FedeJack06/RadioWeatherStation/Schematics/Schematic_master.kicad_sch

## KiCad design Schematics/Schematic_master.kicad_sch (2022-10-13)

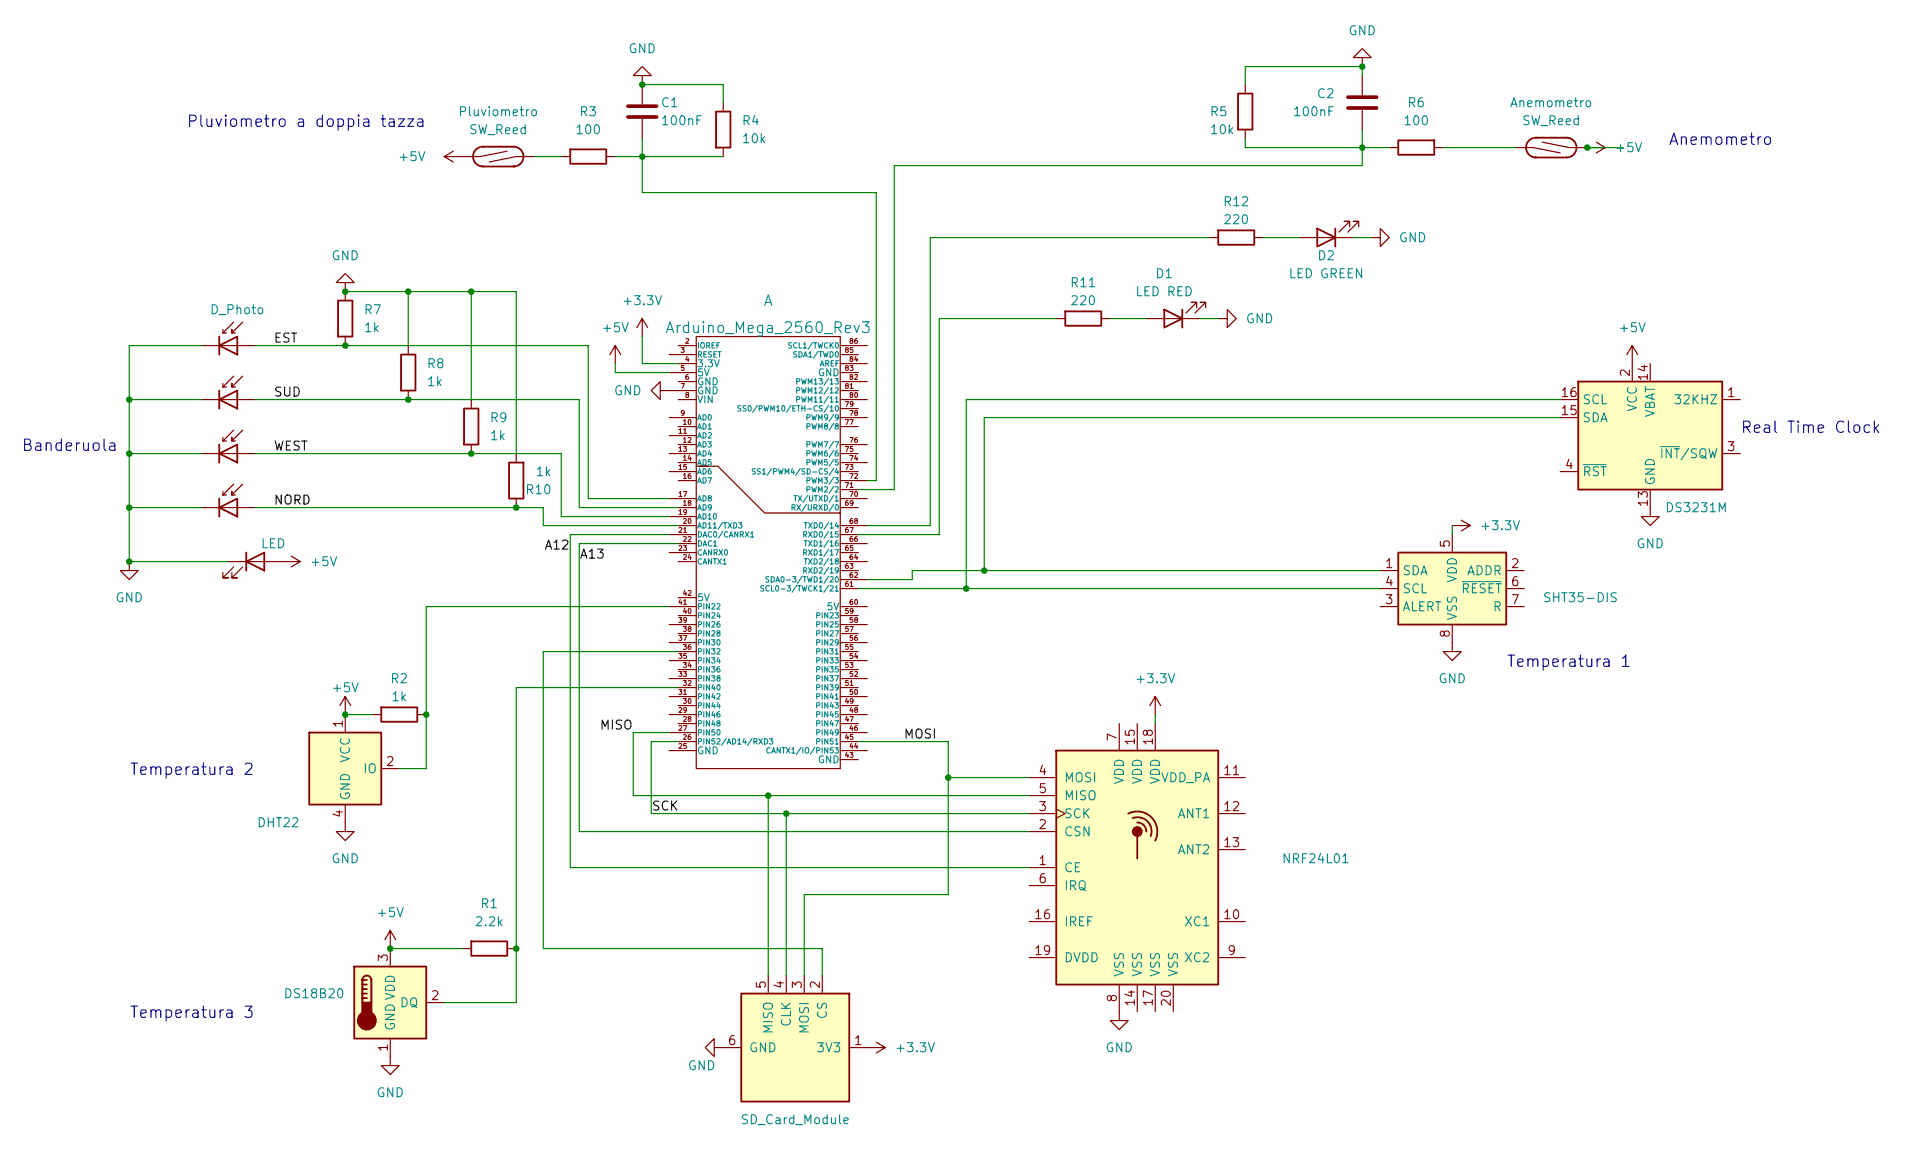
[picture p2: schematic Schematic_master.kicad_sch]

Parts:
A: Arduino_Mega_2560_Rev3
Anemometro: SW_Reed
C1, C2: 100nF
D1: LED RED
D2: LED GREEN
DHT22: DHT22; Aosong_DHT11_5.5x12.0_P2.54mm
DS18B20: DS18B20; TO-92_Inline
DS3231M: DS3231M; SOIC-16W_7.5x10.3mm_P1.27mm
NRF24L01: NRF24L01; QFN-20-1EP_4x4mm_P0.5mm_EP2.5x2.5mm
Pluviometro: SW_Reed
R1: 2.2k
R2, R7, R8, R9, R10: 1k
R3, R6: 100
R4, R5: 10k
R11, R12: 220
SD_Card_Module: SD_Card_Module
SHT35-DIS: SHT35-DIS; Sensirion_DFN-8-1EP_2.5x2.5mm_P0.5mm_EP1.1x1.7mm

Connections:
A12: A.21 (DAC0/CANRX1), NRF24L01.1 (CE)
A13: A.22 (DAC1), NRF24L01.2 (CSN)
EST: A.17 (AD8), R7.2
MISO: A.27 (PIN50), NRF24L01.5 (MISO), SD_Card_Module.5 (MISO)
MOSI: A.45 (PIN51), NRF24L01.4 (MOSI), SD_Card_Module.3 (MOSI)
NORD: A.20 (AD11/TXD3), R10.1
unnamed: A.32 (PIN40), DS18B20.2 (DQ), R1.1
unnamed: A.36 (PIN32), SD_Card_Module.2 (CS)
unnamed: A.41 (PIN22), DHT22.2 (IO), R2.1
unnamed: A.61 (SCL0-3/TWCK1/21), DS3231M.16 (SCL), SHT35-DIS.4 (SCL)
unnamed: A.62 (SDA0-3/TWD1/20), DS3231M.15 (SDA), SHT35-DIS.1 (SDA)
unnamed: A.67 (RXD0/15), R11.2
unnamed: A.68 (TXD0/14), R12.2
unnamed: A.71 (PWM2/2), C2.2, R5.2, R6.1
unnamed: A.72 (PWM3/3), C1.2, R3.1, R4.2
unnamed: Anemometro.2, R6.2
unnamed: C1.1, R4.1
unnamed: C2.1, R5.1
unnamed: D1.2 (A), R11.1
unnamed: D2.2 (A), R12.1
unnamed: DHT22.1 (VCC), R2.2
unnamed: DS18B20.3 (VDD), R1.2
unnamed: DS3231M.5 (GND), DS3231M.6 (GND), DS3231M.7 (GND), DS3231M.8 (GND), DS3231M.9 (GND), DS3231M.10 (GND), DS3231M.11 (GND), DS3231M.12 (GND), DS3231M.13 (GND)
unnamed: Pluviometro.2, R3.2
unnamed: R7.1, R8.1, R9.1, R10.2
unnamed: SHT35-DIS.8 (VSS), SHT35-DIS.9 (VSS)
SCK: A.26 (PIN52/AD14/RXD3), NRF24L01.3 (SCK), SD_Card_Module.4 (CLK)
SUD: A.18 (AD9), R8.2
WEST: A.19 (AD10), R9.2

Notes on the sheet:
Banderuola
Pluviometro a doppia tazza
Temperatura 2
Temperatura 3
Temperatura 1
Anemometro
Real Time Clock
